WSU-4110/Live-Sports-Display/Logo and Name Tags/Name Tags Timothy.stl

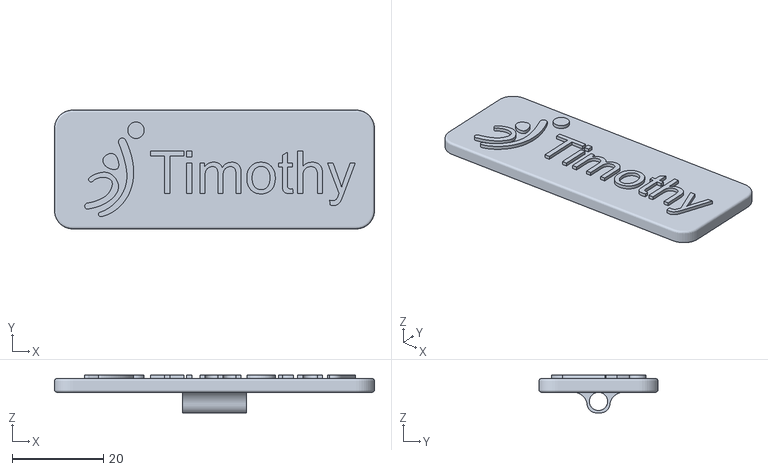
[picture p17: CAD file, 2024-04-19]
Logo and Name Tags/Name Tags Timothy.stl
70.0 x 26.0 x 8.25
