WSU-4110/Live-Sports-Display/Hardware Documentation/8x96 LED Display Cad Files/Print 09APR2024/back panel 2-4 sections 09APR2024.stl

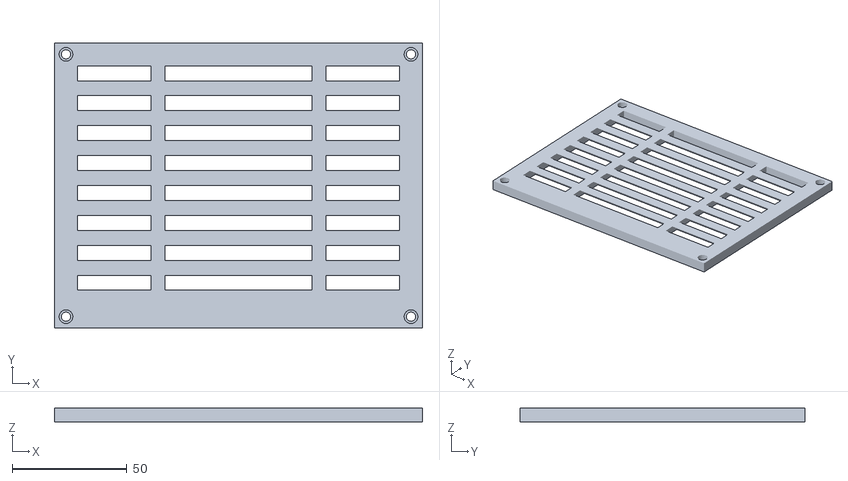
[picture p18: CAD file, 2024-04-19]
Hardware Documentation/8x96 LED Display Cad Files/Print 09APR2024/back panel 2-4 sections 09APR2024.stl
160.2 x 124.2 x 6.00
