WSU-4110/Live-Sports-Display/Hardware Documentation/8x96 LED Display Cad Files/Support Brackets.stl

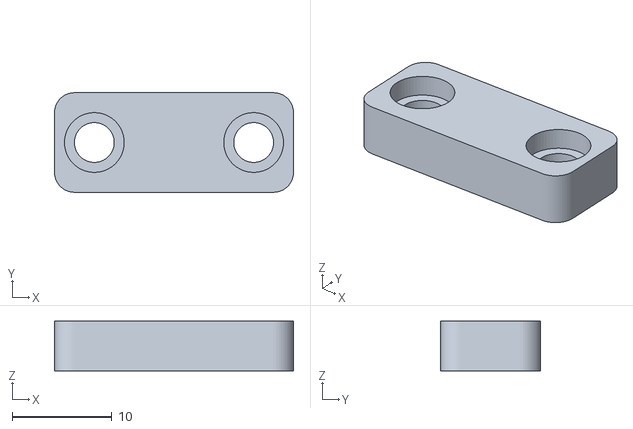
[picture p19: CAD file, 2024-04-19]
Hardware Documentation/8x96 LED Display Cad Files/Support Brackets.stl
24.0 x 10.0 x 5.00
