WSU-4110/Live-Sports-Display/Logo and Name Tags/Name Tag V3 Ayman_.stl

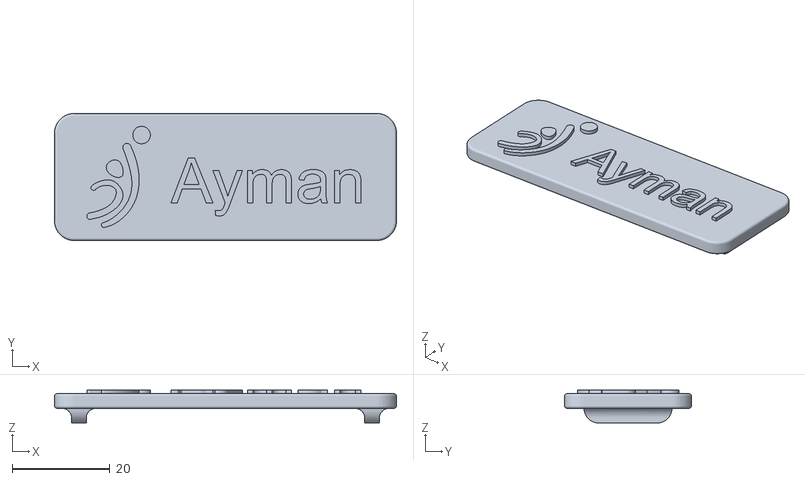
[picture p20: CAD file, 2024-04-19]
Logo and Name Tags/Name Tag V3 Ayman_.stl
70.0 x 26.0 x 6.75
