WSU-4110/Live-Sports-Display/Logo and Name Tags/Name Tag V3 Title 1.75.stl

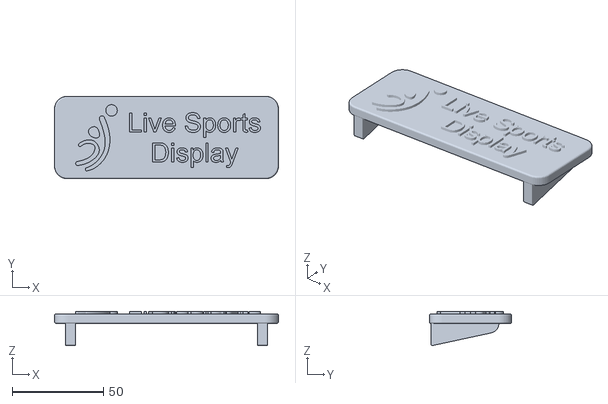
[picture p21: CAD file, 2024-04-19]
Logo and Name Tags/Name Tag V3 Title 1.75.stl
122.5 x 45.1 x 18.6
