WSU-4110/Live-Sports-Display/Hardware Documentation/64x128 LED Display Cad Files/Version 4/64x64 LED Display Cover - Right Side 16MAR2024.stl

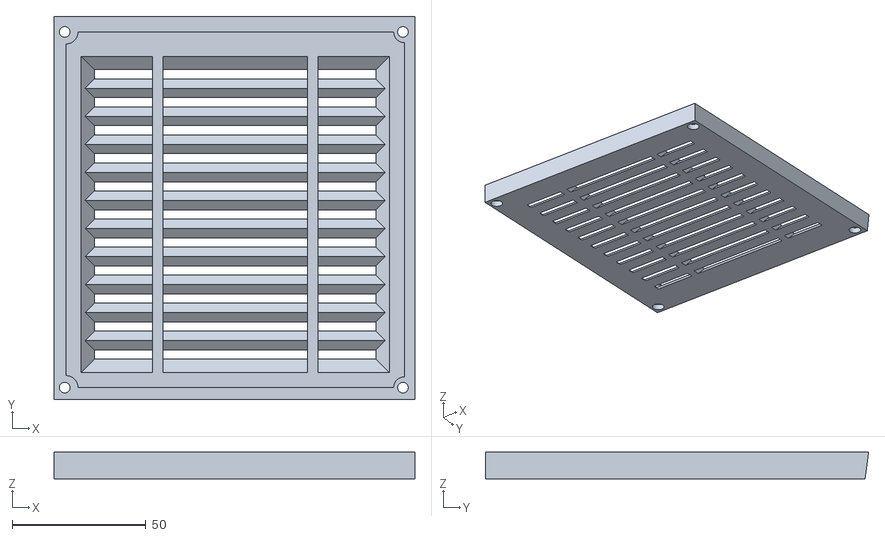
[picture p22: CAD file, 2024-03-27]
Hardware Documentation/64x128 LED Display Cad Files/Version 4/64x64 LED Display Cover - Right Side 16MAR2024.stl
135.0 x 143.3 x 10.0
