WSU-4110/Live-Sports-Display/Logo and Name Tags/Plate with Logo, Live Sports Display v1.stl

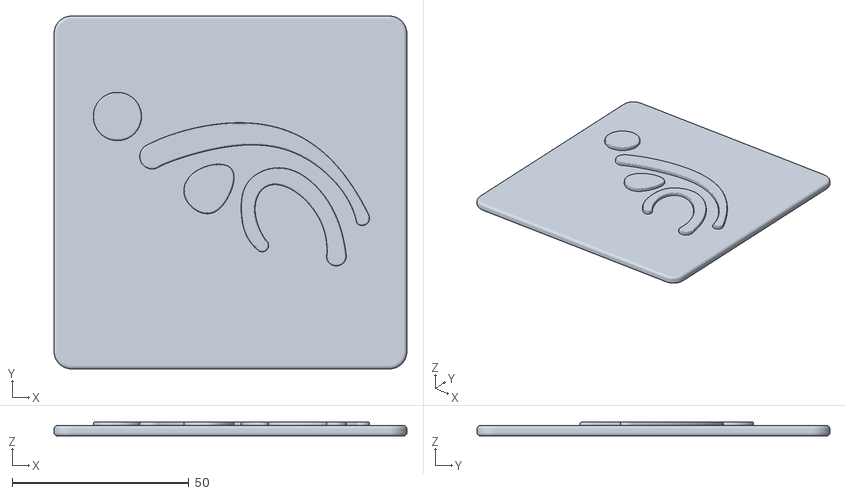
[picture p23: CAD file, 2024-04-19]
Logo and Name Tags/Plate with Logo, Live Sports Display v1.stl
100.0 x 100.0 x 4.00
