WSU-4110/Live-Sports-Display/Hardware Documentation/8x96 LED Display Cad Files/Cross Section 2 of 6 (31MAR2024).3mf

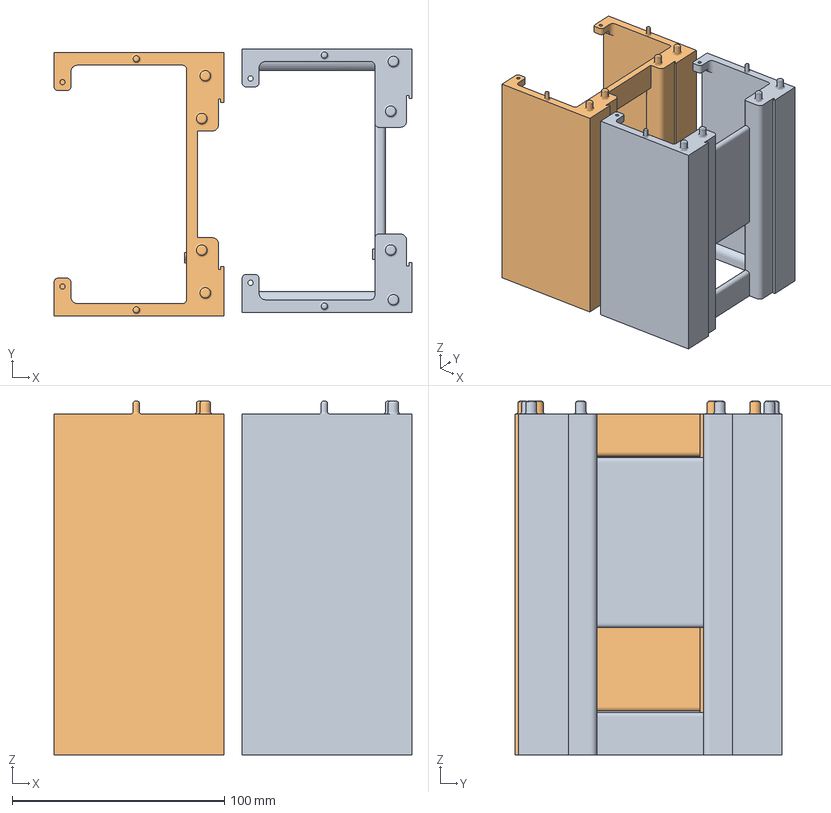
[picture p24: CAD file, 2024-04-19]
Hardware Documentation/8x96 LED Display Cad Files/Cross Section 2 of 6 (31MAR2024).3mf
168.6 x 125.9 x 166.6 mm
Cross Section 1 of 6 (31MAR2024).stl
Cross Section 2 of 6 (31MAR2024).stl
