WSU-4110/Live-Sports-Display/Logo and Name Tags/Name Tag V3 Rory v0.stl

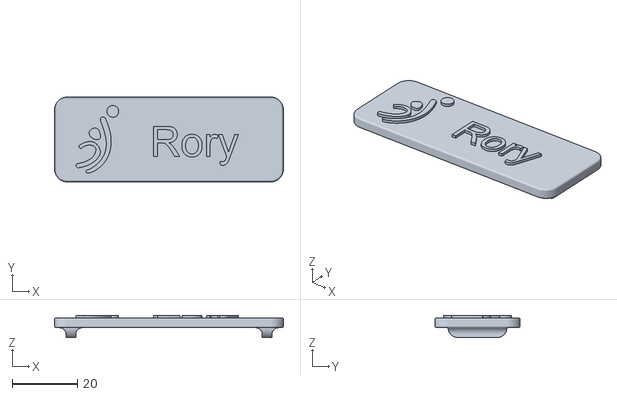
[picture p25: CAD file, 2024-04-19]
Logo and Name Tags/Name Tag V3 Rory v0.stl
70.0 x 26.0 x 6.75
