WSU-4110/Live-Sports-Display/Hardware Documentation/8x96 LED Display Cad Files/Cross Section 1 of 6 (31MAR2024).stl

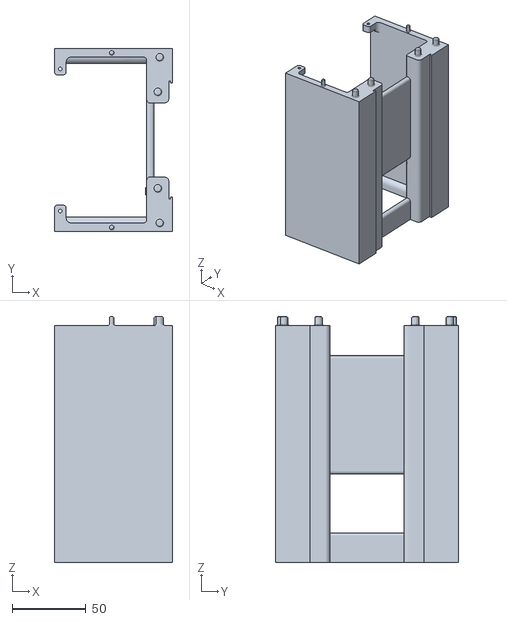
[picture p26: CAD file, 2024-04-19]
Hardware Documentation/8x96 LED Display Cad Files/Cross Section 1 of 6 (31MAR2024).stl
80.0 x 124.2 x 166.6
