WSU-4110/Live-Sports-Display/Hardware Documentation/8x96 LED Display Cad Files/Test Spacer Version 4.stl

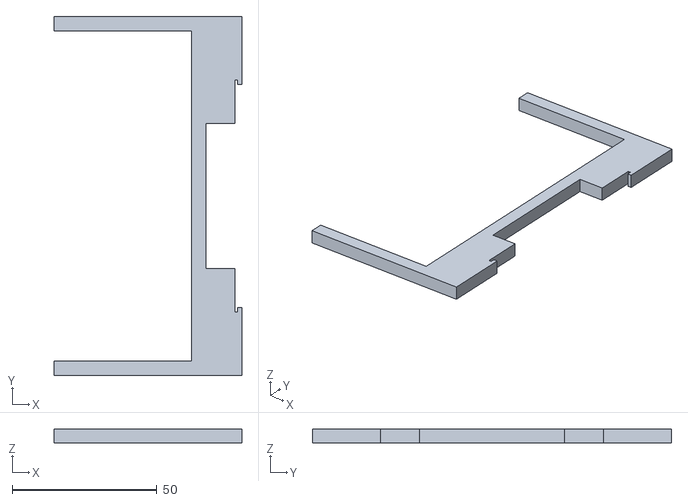
[picture p27: CAD file, 2024-04-19]
Hardware Documentation/8x96 LED Display Cad Files/Test Spacer Version 4.stl
65.0 x 124.2 x 5.00
