WSU-4110/Live-Sports-Display/Logo and Name Tags/Name Tags Timothy v3.stl

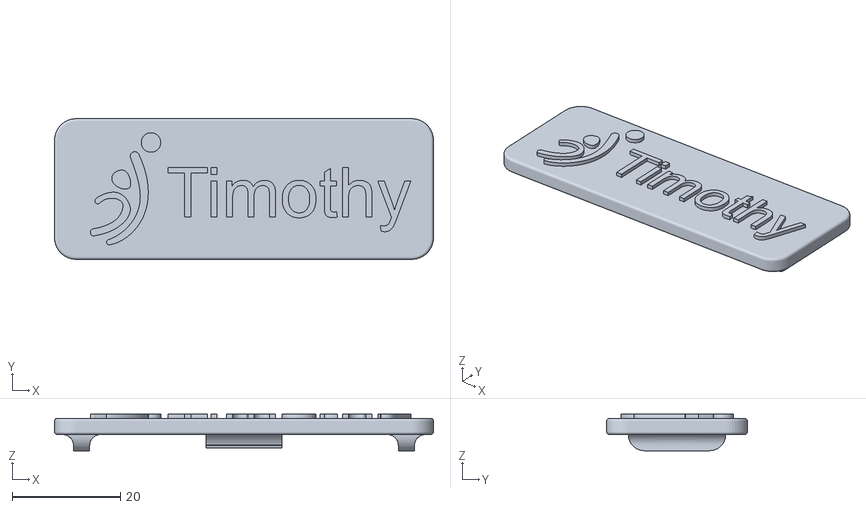
[picture p28: CAD file, 2024-04-19]
Logo and Name Tags/Name Tags Timothy v3.stl
70.0 x 26.0 x 6.75
