WSU-4110/Live-Sports-Display/Logo and Name Tags/Name Tag V3 Mitchell v1.stl

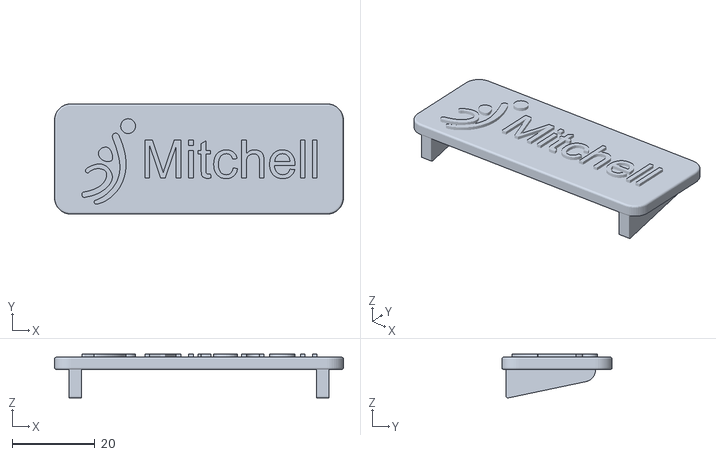
[picture p29: CAD file, 2024-04-19]
Logo and Name Tags/Name Tag V3 Mitchell v1.stl
70.0 x 26.8 x 10.6
