WSU-4110/Live-Sports-Display/Website/media/test.png

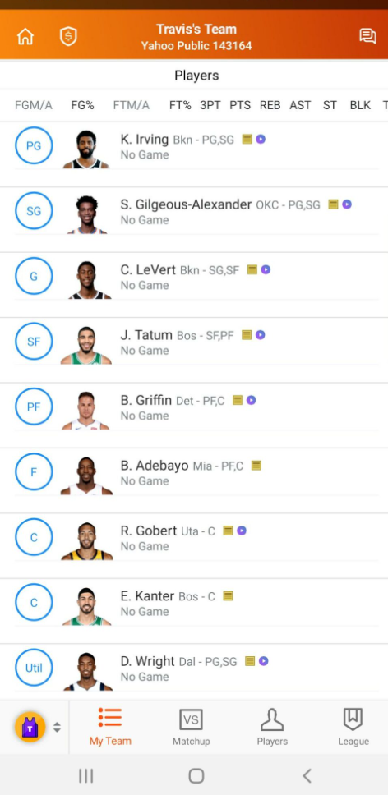
Website/media/test.png
